mmakaay/dsmr-reader-for-esphome/images/PCB_with_display.png

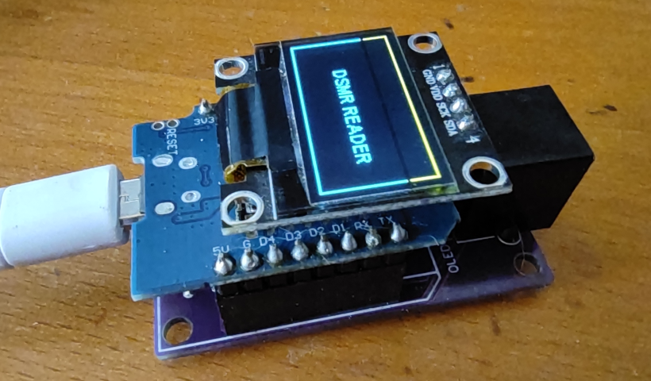
images/PCB_with_display.png
