mmakaay/dsmr-reader-for-esphome/PCB/design.png

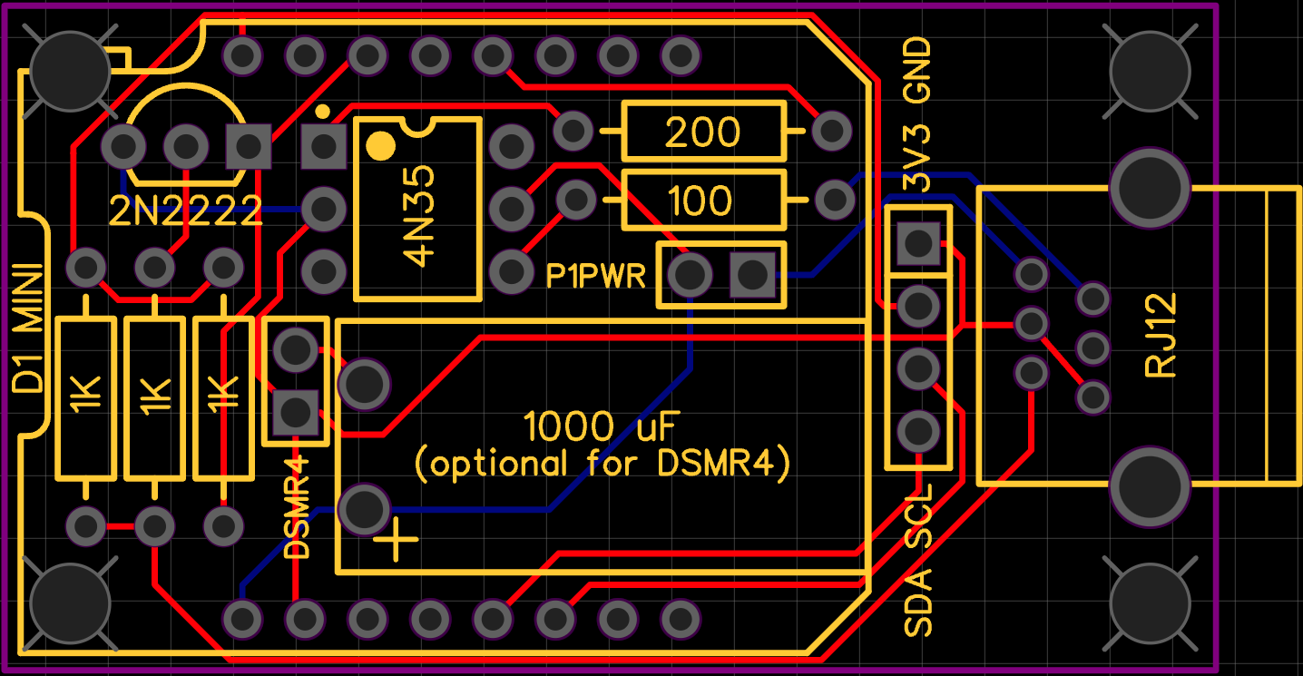
PCB/design.png
