mmakaay/dsmr-reader-for-esphome/PCB/schematic.png

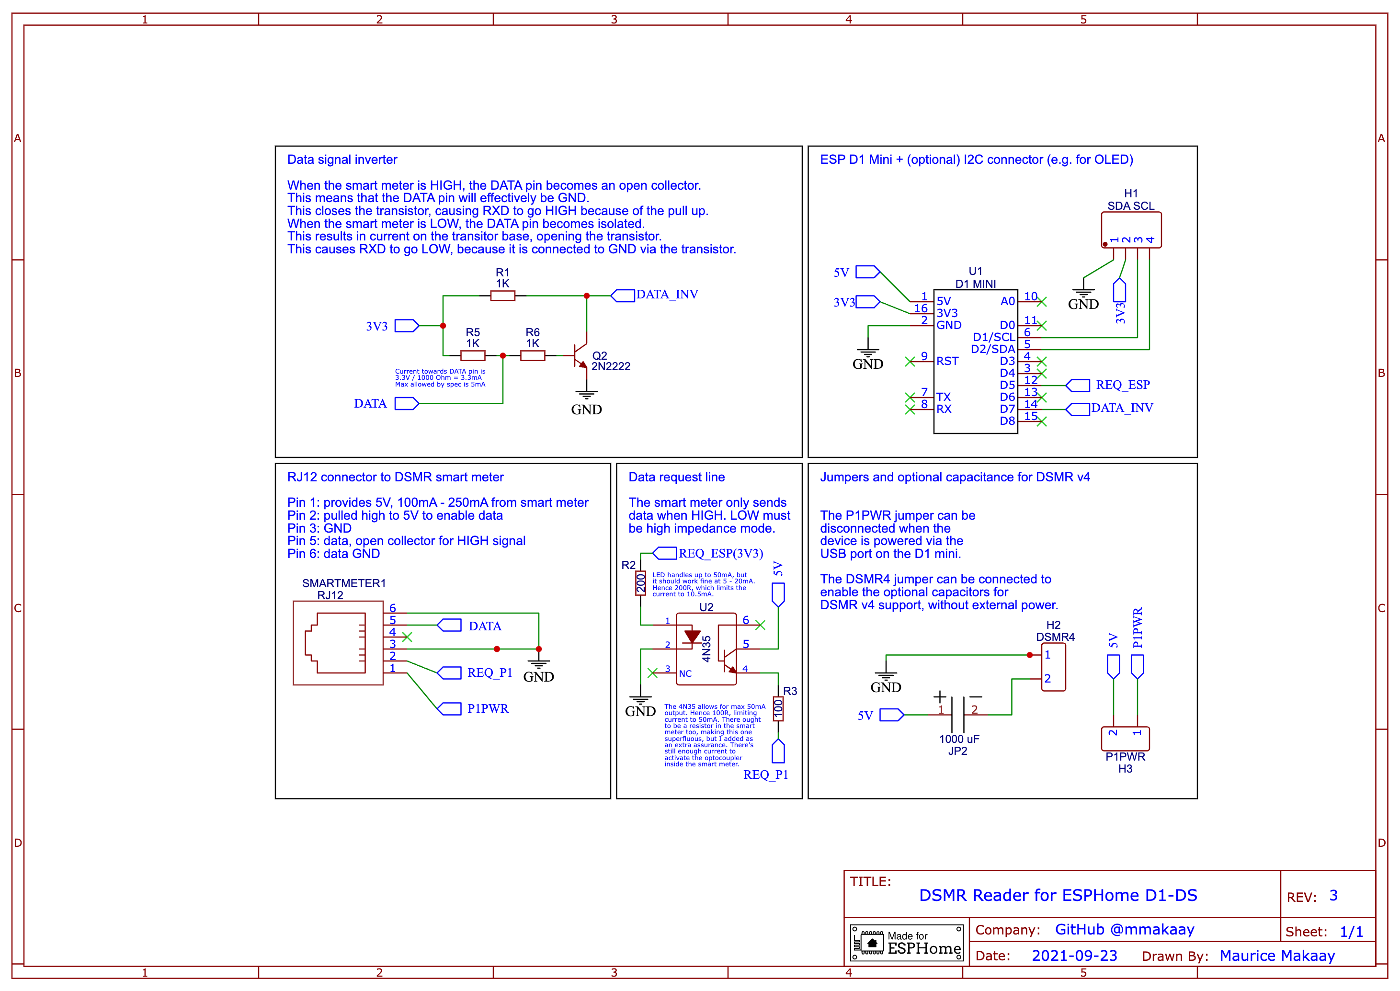
PCB/schematic.png
