mmakaay/dsmr-reader-for-esphome/images/build/02_empty_PCB.jpg

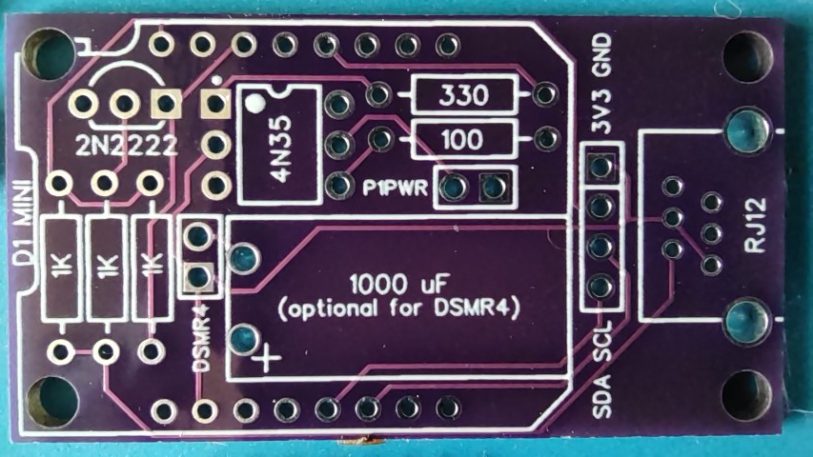
images/build/02_empty_PCB.jpg
