mmakaay/dsmr-reader-for-esphome/images/build/03_d1_headers_a.jpg

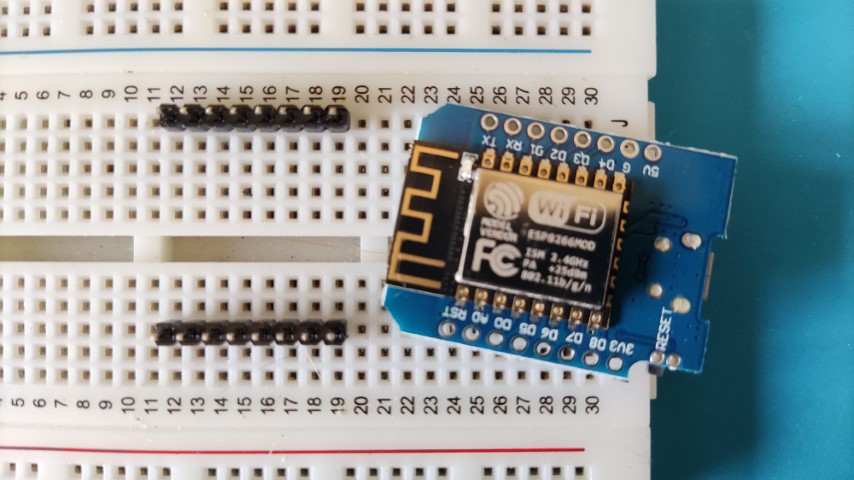
images/build/03_d1_headers_a.jpg
