mmakaay/dsmr-reader-for-esphome/images/build/04_d1_headers_b.jpg

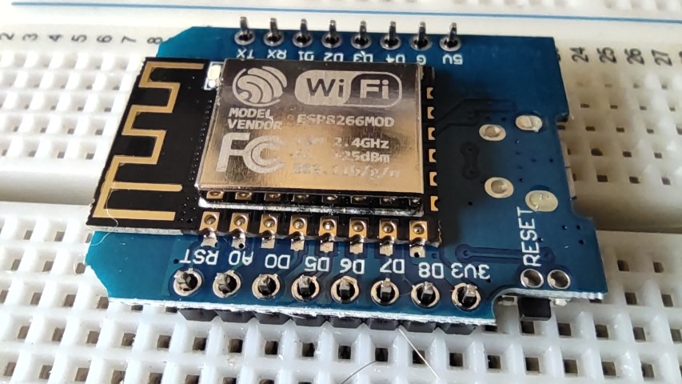
images/build/04_d1_headers_b.jpg
