mmakaay/dsmr-reader-for-esphome/images/build/07_3xresistor_1k_b.jpg

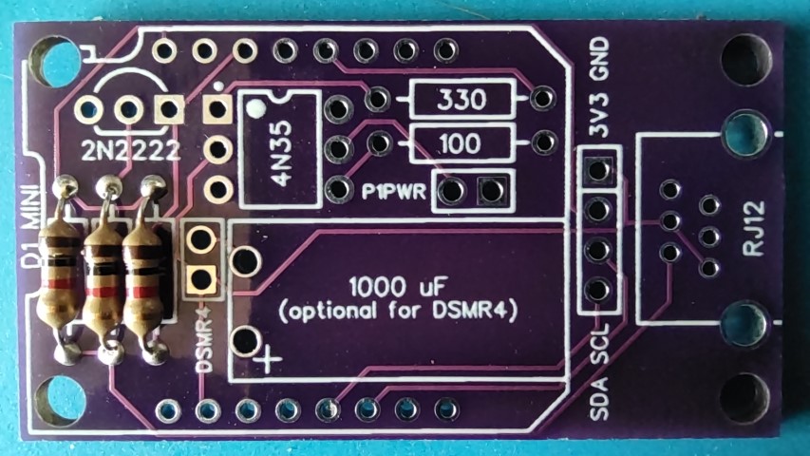
images/build/07_3xresistor_1k_b.jpg
