mmakaay/dsmr-reader-for-esphome/images/build/08_resistors_330R_and_100R.jpg

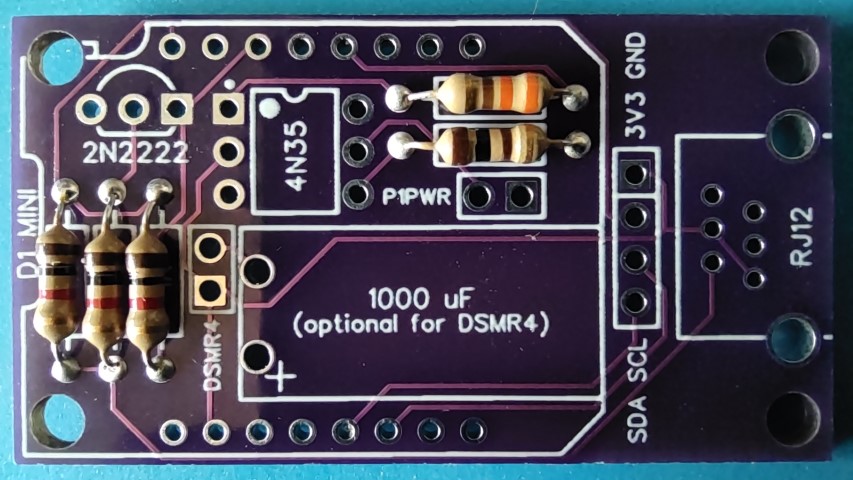
images/build/08_resistors_330R_and_100R.jpg
