mmakaay/dsmr-reader-for-esphome/images/build/10_octocoupler.jpg

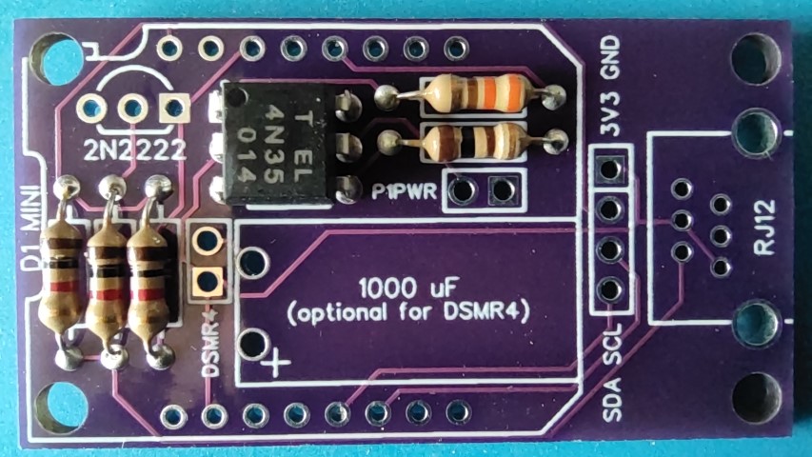
images/build/10_octocoupler.jpg
