mmakaay/dsmr-reader-for-esphome/images/build/11_jumper_headers.jpg

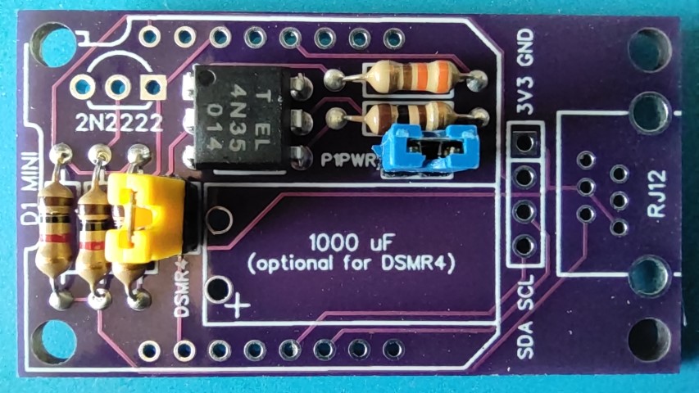
images/build/11_jumper_headers.jpg
