mmakaay/dsmr-reader-for-esphome/images/build/12_transistor_2N2222.jpg

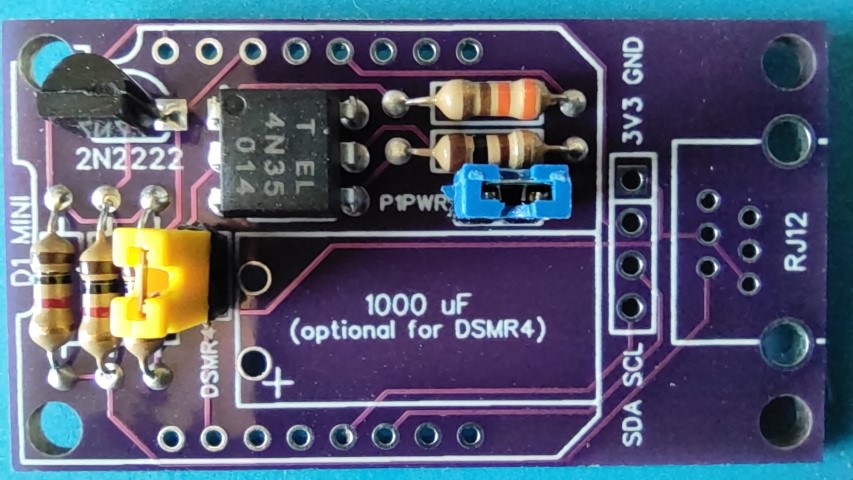
images/build/12_transistor_2N2222.jpg
