mmakaay/dsmr-reader-for-esphome/images/build/13_capacitor_1000uF_a.jpg

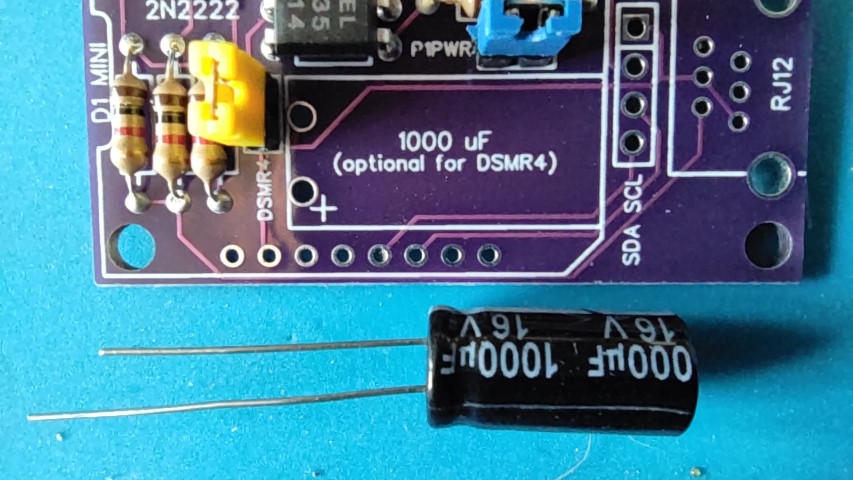
images/build/13_capacitor_1000uF_a.jpg
