mmakaay/dsmr-reader-for-esphome/images/build/14_capacitor_1000uF_b.jpg

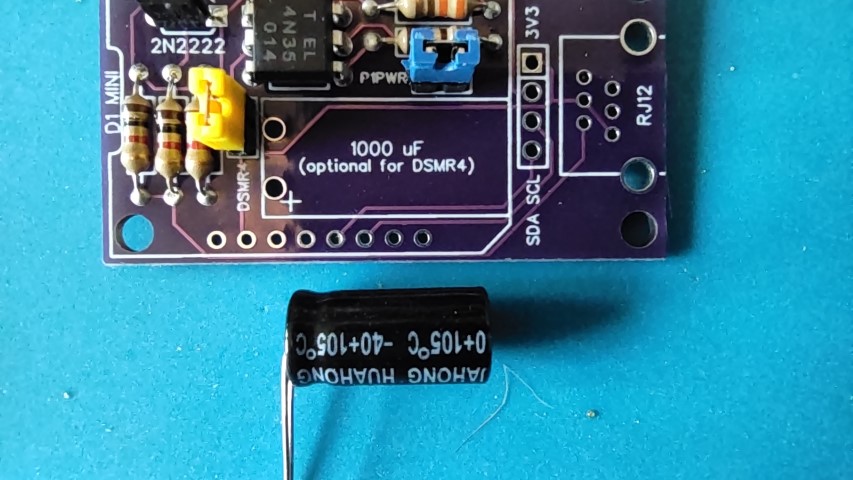
images/build/14_capacitor_1000uF_b.jpg
