mmakaay/dsmr-reader-for-esphome/images/build/15_capacitor_1000uF_c.jpg

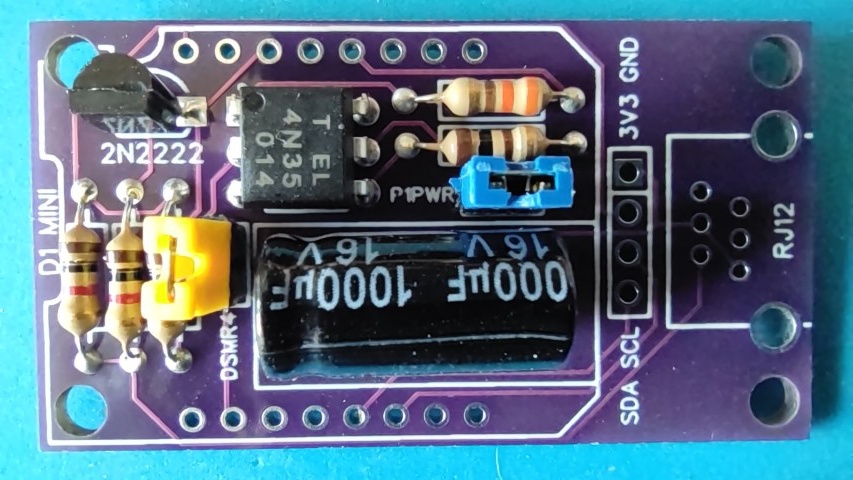
images/build/15_capacitor_1000uF_c.jpg
