mmakaay/dsmr-reader-for-esphome/images/build/17_D1_female_headers_b.jpg

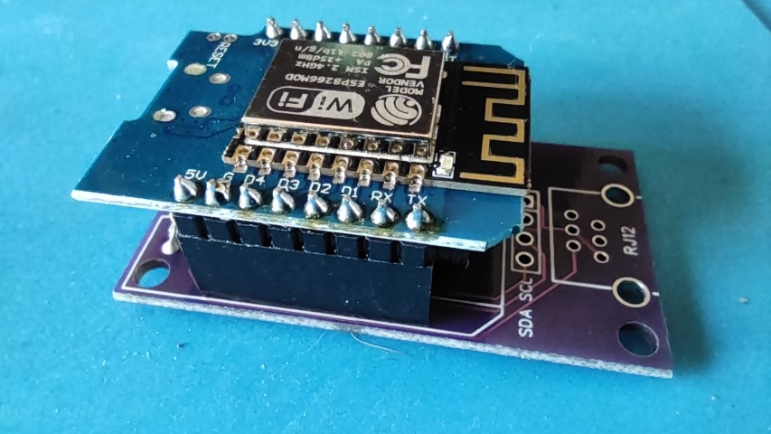
images/build/17_D1_female_headers_b.jpg
