mmakaay/dsmr-reader-for-esphome/images/build/18_D1_female_headers_c.jpg

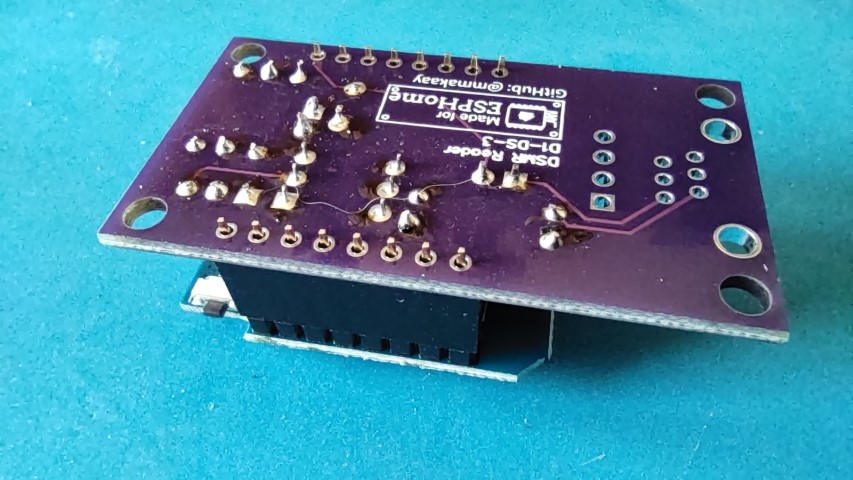
images/build/18_D1_female_headers_c.jpg
