mmakaay/dsmr-reader-for-esphome/images/build/19_D1_female_headers_d.jpg

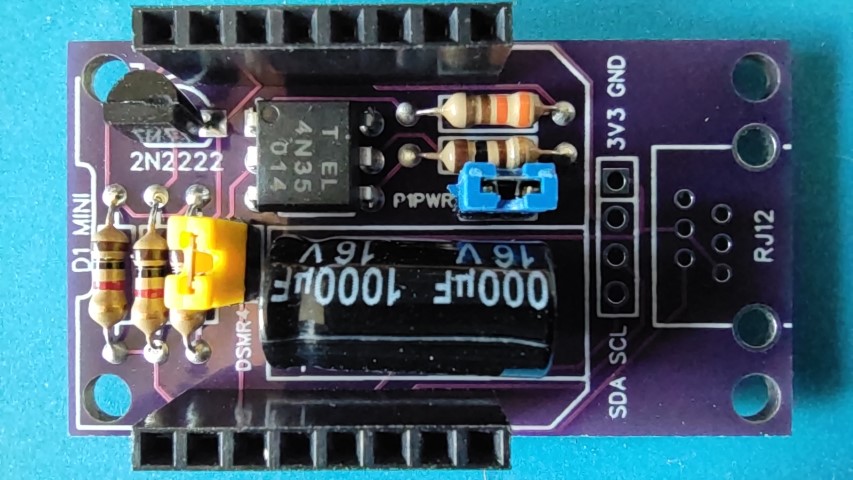
images/build/19_D1_female_headers_d.jpg
