mmakaay/dsmr-reader-for-esphome/images/build/20_OLED_female_header_a.jpg

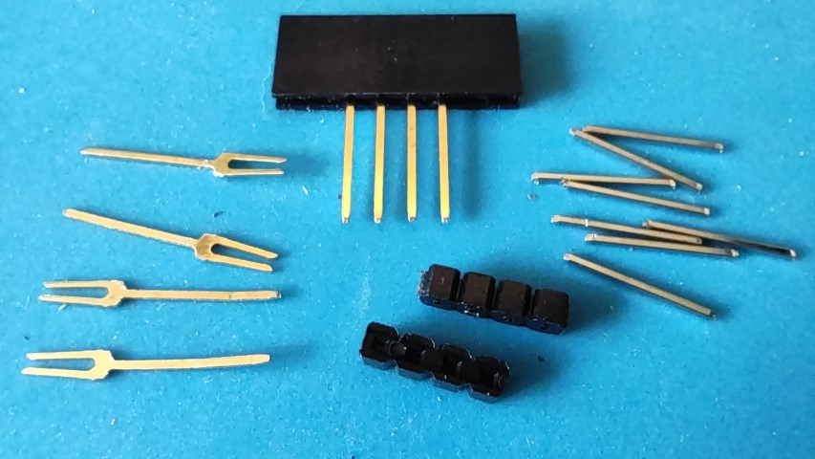
images/build/20_OLED_female_header_a.jpg
