mmakaay/dsmr-reader-for-esphome/images/build/21_OLED_female_header_b.jpg

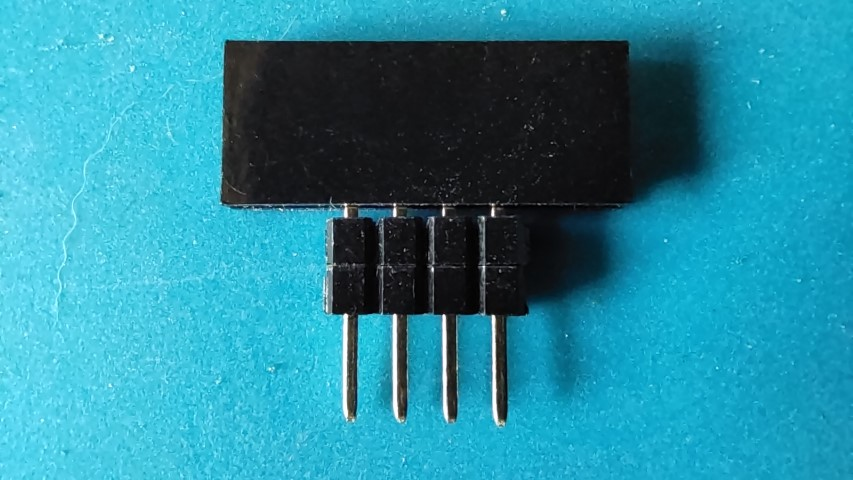
images/build/21_OLED_female_header_b.jpg
