mmakaay/dsmr-reader-for-esphome/images/build/22_OLED_female_header_c.jpg

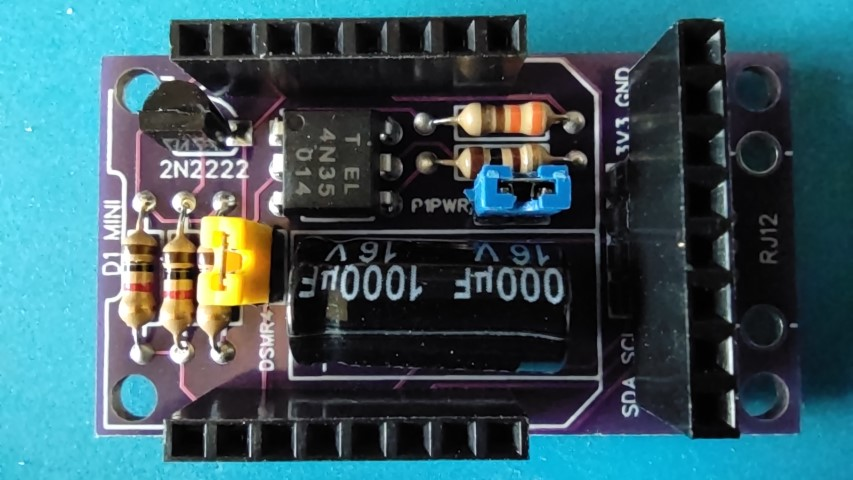
images/build/22_OLED_female_header_c.jpg
