mmakaay/dsmr-reader-for-esphome/images/build/23_OLED_female_header_d.jpg

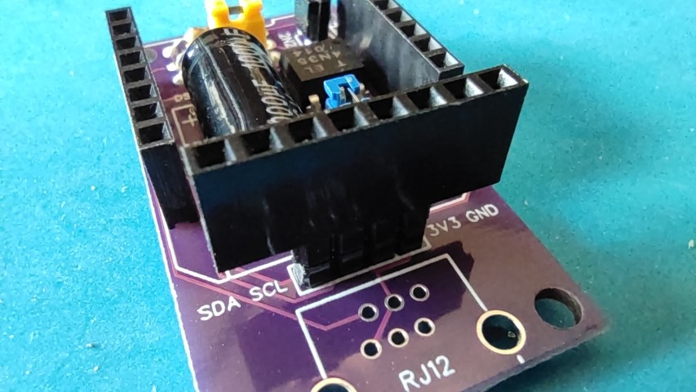
images/build/23_OLED_female_header_d.jpg
