mmakaay/dsmr-reader-for-esphome/images/build/24_RJ12_socket_a.jpg

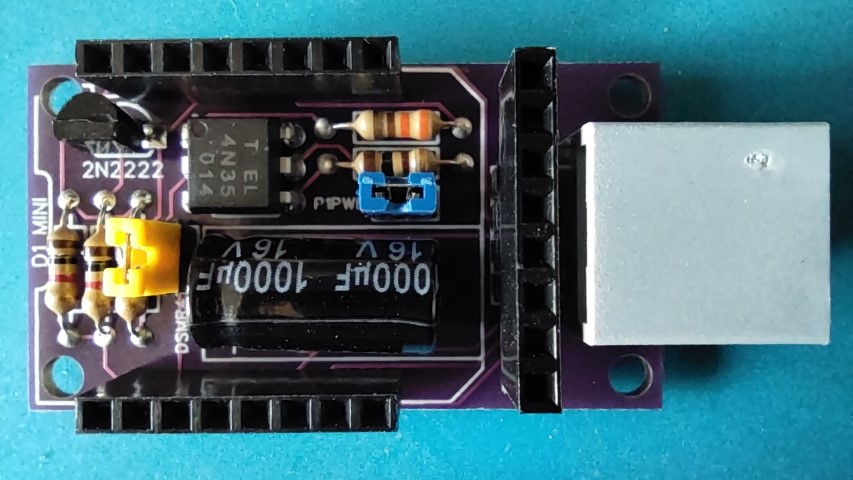
images/build/24_RJ12_socket_a.jpg
