mmakaay/dsmr-reader-for-esphome/images/build/25_RJ12_socket_b.jpg

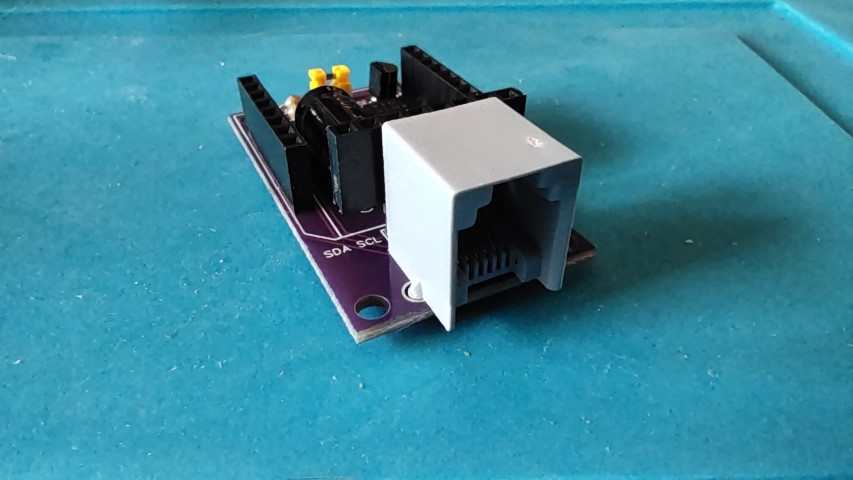
images/build/25_RJ12_socket_b.jpg
