mmakaay/dsmr-reader-for-esphome/images/build/26_D1_assembled_a.jpg

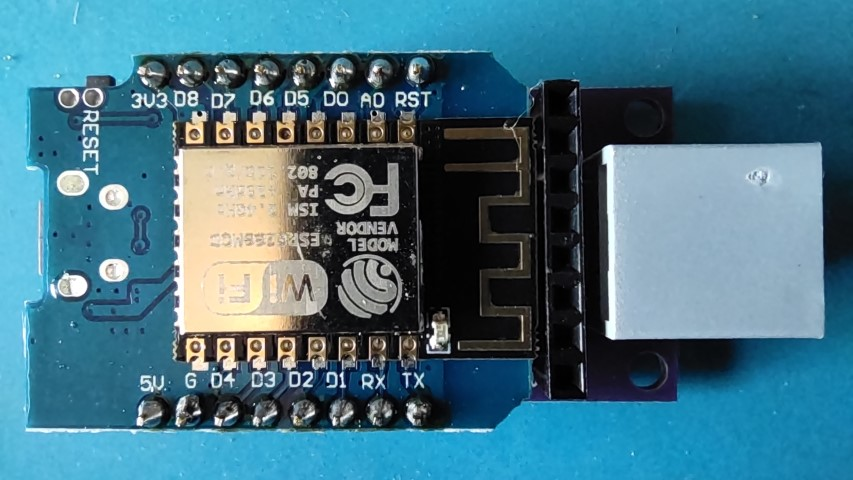
images/build/26_D1_assembled_a.jpg
