mmakaay/dsmr-reader-for-esphome/images/build/27_D1_assembled_b.jpg

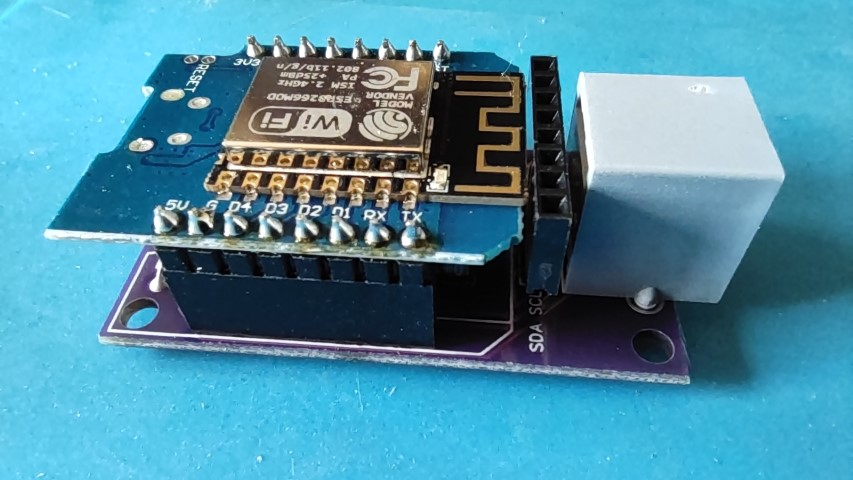
images/build/27_D1_assembled_b.jpg
