mmakaay/dsmr-reader-for-esphome/images/build/28_OLED_dispay_a.jpg

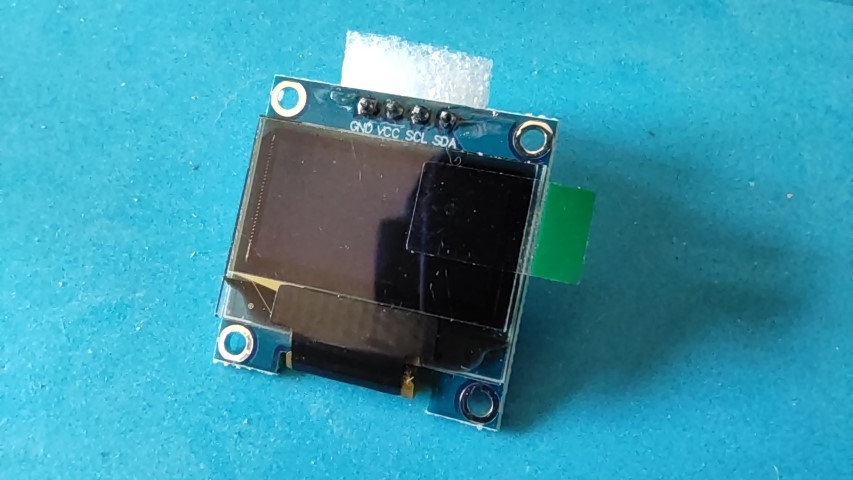
images/build/28_OLED_dispay_a.jpg
