mmakaay/dsmr-reader-for-esphome/images/build/29_OLED_dispay_b.jpg

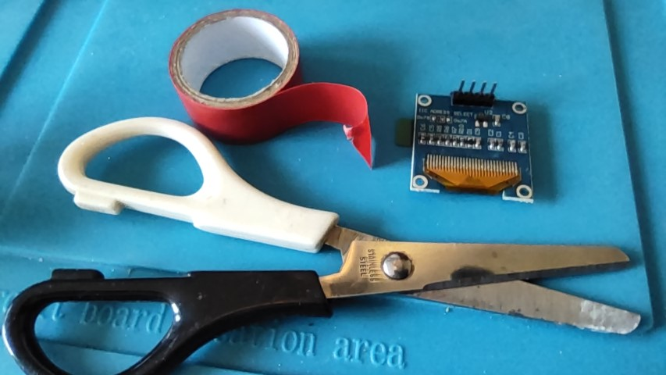
images/build/29_OLED_dispay_b.jpg
