mmakaay/dsmr-reader-for-esphome/images/build/31_fully_assembled.jpg

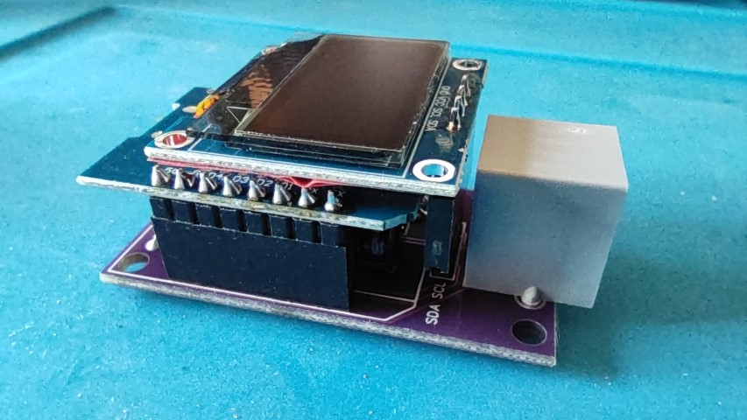
images/build/31_fully_assembled.jpg
