mmakaay/dsmr-reader-for-esphome/images/PCB_soldered.jpg

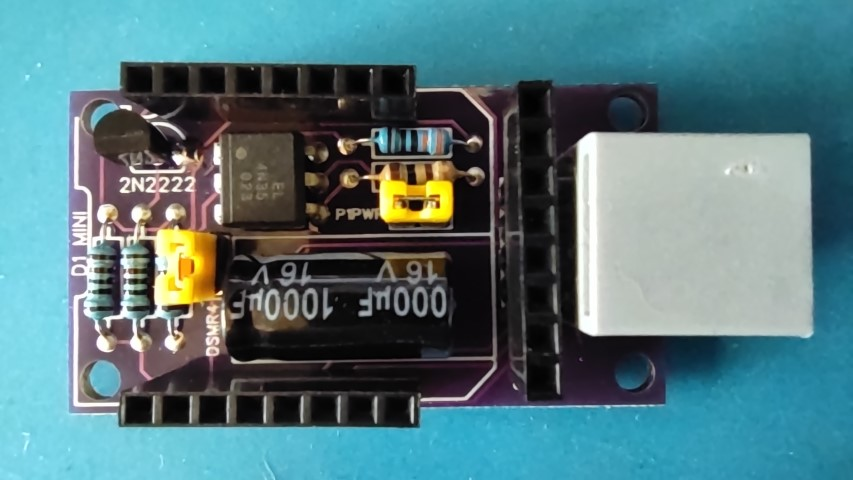
images/PCB_soldered.jpg
